JaviElio/Geek-Spinner/Firmware/textAndShapes.h

// Place data (except text[]) in program memory to save dynamic memory
// https://playground.arduino.cc/Main/PROGMEM
// http://www.gammon.com.au/progmem

const char upperText[]  = "Geek";
const char lowerText[]  = "Spinner";
const char rpmText[]    = "RPM";   
const char revText[]    = "REV";

const char PROGMEM shape_1[] = { // heart
  0x80,
  0x80,
  0x80,
  0x40,
  0x40,
  0x20,
  0x10,
  0x08,
  0x04,
  0x02,
  0x01,
  0x01,
  0x02,
  0x04,
  0x08,
  0x10,
  0x20,
  0x40,
  0x80,
  0x80,
  0x80,
  0x80,
  0x80,
  0x40,
  0x40,
  0x40,
  0x20,
  0x20,
  0x20,
  0x20,
  0x10,
  0x10,
  0x10,
  0x10,
  0x10,
  0x10,
  0x10,
  0x10,
  0x10,
  0x10,
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
};
 

const char PROGMEM shape_2[] = { // smile
  0x01,
  0x31,
  0x79,
  0x79,
  0x31,
  0x01,
  0x01,
  0x01,
  0x01,
  0x01, 
  0x01,
  0x01,
  0x01,
  0x01,
  0x01,
  0x31,
  0x79,
  0x79,
  0x31,
  0x01,
  0x01,
  0x01,
  0x01,
  0x01,
  0x01,
  0x01,
  0x01,
  0x01,
  0x01,
  0x01,
  0x01,
  0x01,
  0x01,
  0x01,
  0x21,
  0x21,
  0x21,
  0x21,
  0x21,
  0x21,
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
};

const char PROGMEM shape_3[] = { //fan
	0x01,
	0x02,
	0x04,
	0x08,
	0x10,
	0x20,
	0x20,
	0x40,
	0x40,
	0x80,
	0x80,
	0x80,
	0x01,
	0x02,
	0x04,
	0x08,
	0x10,
	0x20,
	0x20,
	0x40,
	0x40,
	0x80,
	0x80,
	0x80,
	0x01,
	0x02,
	0x04,
	0x08,
	0x10,
	0x20,
	0x20,
	0x40,
	0x40,
	0x80,
	0x80,
	0x80,
	0x01,
	0x02,
	0x04,
	0x08,
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
};
